ChrisBrinton/SensorIoT-GW/firmware/src/mqtt.ino

 /*

MQTT MODULE

Copyright (C) 2016-2017 by Xose Pérez <xose dot perez at gmail dot com>

*/

#include <ESP8266WiFi.h>
#include <AsyncMqttClient.h>
#include "config/all.h"

AsyncMqttClient mqtt;
unsigned int connectTries = 0;

// -----------------------------------------------------------------------------
// MQTT
// -----------------------------------------------------------------------------

bool mqttConnected() {
    return mqtt.connected();
}

void mqttDisconnect() {
    mqtt.disconnect();
}

void mqttSend(char * topic, char * message) {
    if (!mqtt.connected()) return;
    DEBUG_MSG("[MQTT] Sending %s%s\n", topic, message);
    if(!mqtt.publish(topic, MQTT_QOS, MQTT_RETAIN, message)) {
        DEBUG_MSG("[MQTT] Send failed!\n");
    };
}

void _mqttOnConnect(bool sessionPresent) {

    DEBUG_MSG("[MQTT] Connected!\n");
    connectTries = 0;
    // Send status via webSocket
    wsSend((char *) "{\"mqttStatus\": true}");

    String sTopic = getSetting("ipTopic", MQTT_IP_TOPIC);
    String tmpHN = String(getSetting("hostname", APP_NAME));
    tmpHN.replace("_","/");
    sTopic.replace("{hostname}", tmpHN);

    // Say hello and report our IP and VERSION
    mqttSend((char *) sTopic.c_str(), (char *) getIP().c_str());

    // Subscribe to the reply topic from the server at QoS 0 (0=almost once, 1=AtleastOnce, 2=ExactlyOnce)
    String replyTopic = getSetting("mqttReplyTopic", MQTT_REPLY_TOPIC);
    replyTopic.replace("{hostname}", tmpHN);
    mqtt.subscribe(replyTopic.c_str(), 1);
    DEBUG_MSG("[MQTT] subscribed to reply topic: %s\n", replyTopic.c_str());


}

void _mqttOnDisconnect(AsyncMqttClientDisconnectReason reason) {

    // Send status via webSocket
    wsSend((char *) "{\"mqttStatus\": false}");
    DEBUG_MSG("[MQTT] Disconnected!!! Reason:%i\n", reason);

}

char* _returnVal;
void _onMqttMessage(char* topic, char* payload, AsyncMqttClientMessageProperties properties, size_t len, size_t index, size_t total) {

    //Complete messages may not arrive in a single call to _onMqttMessage(). We need to watch len, index and total to determine this
    //if len != total then the message will arrive in pieces. We use index to determine which chunk of the message this piece is.
    if(index==0) { //start of a new message
        _returnVal = new char[total+1];
    }
    char* buff = _returnVal + index;
    memcpy(buff, payload, len); //copy this chunk into place
    if(index + len == total) { // this is the final chunk of this message, go ahead and process.
        char* buff = _returnVal + total;
        *buff = '\0';
        DEBUG_MSG("[MQTT] Publish received. topic: %s payload: %s\n", topic, _returnVal);
        DEBUG_MSG("[MQTT] qos: %i dup: %i retain: %i len: %i index: %i total: %i\n", properties.qos, properties.dup, properties.retain, len, index, total);

        processCommandReply(topic, _returnVal);

        free(_returnVal);
    }
}

void mqttConnect() {

    if (!mqtt.connected()) {

        // Last option: reconnect to wifi after MQTT_MAX_TRIES attemps in a row
        static unsigned long last_try = millis();
        if (millis() - last_try < MQTT_TRY_INTERVAL) {
            if (++connectTries >= MQTT_MAX_TRIES) {
                DEBUG_MSG("[MQTT] Failed to connect to MQTT broker. Max tries exceeded\n");
                stageDisplayMsg((char*)"MQTT Connect failed. Restarting");
                wifiDisconnect();
                connectTries = 0;
                setRestartCountdown(15);
                return;
            }
        } else {
            connectTries = 0;
        }
        last_try = millis();

		mqtt.disconnect();

        String host = getSetting("mqttServer", MQTT_SERVER);
        String port = getSetting("mqttPort", String(MQTT_PORT));
        String user = getSetting("mqttUser");
        String pass = getSetting("mqttPassword");
    
		if (host.length() == 0) return;

        DEBUG_MSG("[MQTT] Connecting to broker at %s:%s ", (char *) host.c_str(), (char *) port.c_str());
        //The AsyncMQTT lib doesnt make a copy of the clientID we pass it. To insure that it doesnt
        //change before the connect packet containing the clientID (which happens asynchronousely, duh) is sent,
        //create its own static copy of the string. And yes, that was happening.
        static char* clientID = (char*)malloc(strlen(getSetting("hostname", APP_NAME).c_str()));
        strcpy(clientID, getSetting("hostname", APP_NAME).c_str());
        mqtt.setClientId(clientID);

        mqtt.setServer(host.c_str(), port.toInt());
        mqtt.setKeepAlive(MQTT_KEEPALIVE);
        mqtt.setCleanSession(false);
            //.setWill("topic/online", 2, true, "no")

        if ((user != "") & (pass != "")) {
            DEBUG_MSG(" as user %s with pass |%s|", (char *) user.c_str(), (char *) pass.c_str());
            mqtt.setCredentials(user.c_str(), pass.c_str());
        } else {
            DEBUG_MSG("anonymously");
        }

        DEBUG_MSG(" with ClientID %s\n", clientID);

        mqtt.connect();

    }

}

void mqttSetup() {
    if(getSetting("mqttEnabled", MQTT_ENABLED) == "on") {
        mqtt.onConnect(_mqttOnConnect);
        mqtt.onDisconnect(_mqttOnDisconnect);
        mqtt.onMessage(_onMqttMessage);
    } else
    {
        DEBUG_MSG("[MQTT] MQTT disabled\n");
    }
}

void mqttLoop() {

    static unsigned long lastPeriod = 0;
    if(getSetting("mqttEnabled", MQTT_ENABLED) == "on") {
      if (WiFi.status() == WL_CONNECTED) {
        if (WiFi.getMode() != WIFI_AP) {
          if (!mqtt.connected()) {
          	unsigned long currPeriod = millis() / MQTT_RECONNECT_DELAY;
          	if (currPeriod != lastPeriod) {
          	    lastPeriod = currPeriod;
                  mqttConnect();
            }
          }
        }
      }
    }
}
