ChrisBrinton/SensorIoT-GW/firmware/src/config/version.h

 #define APP_NAME                "GDESGW1"
#define APP_VERSION             "1.1.6"
#define APP_AUTHOR              "cbrinton@gmail.com"
#define APP_WEBSITE             "https://github.com/ChrisBrinton/SensorIoT-GW"
